Matt-Santos/Horizon/documents/Refrences/20104029.jpg

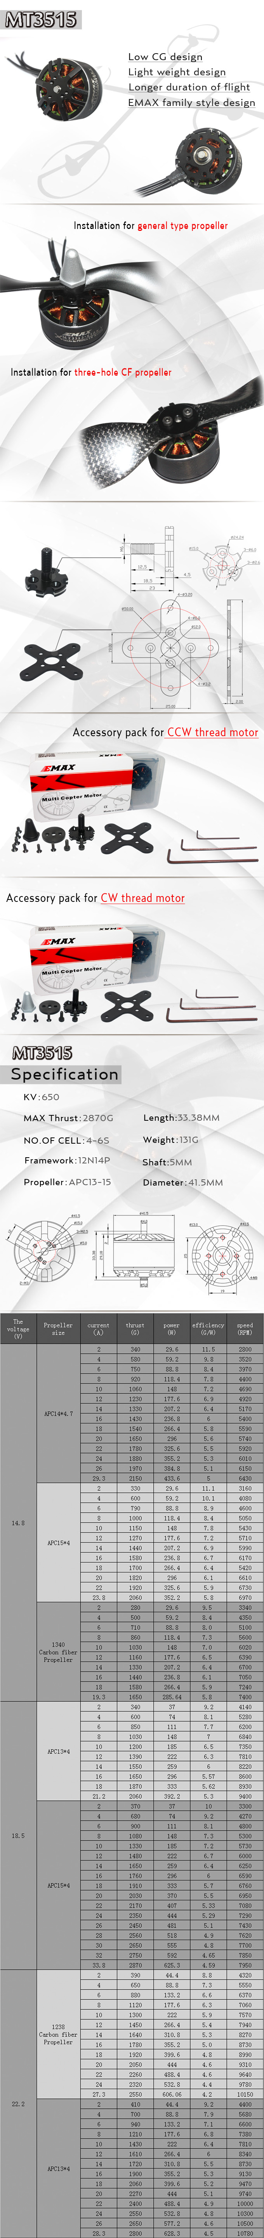
documents/Refrences/20104029.jpg
